jinhwanlazy/hhkb-pcb/firmware/config.h

/*
Copyright 2012 Jun Wako <wakojun@gmail.com>

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
You should have received a copy of the GNU General Public License
along with this program.  If not, see <http://www.gnu.org/licenses/>.
*/

#ifndef CONFIG_H
#define CONFIG_H


/* USB Device descriptor parameter */
#define VENDOR_ID       0xFEED
#define PRODUCT_ID      0x6060
#define DEVICE_VER      0x0001
#define MANUFACTURER    jinhwanlazy
#define PRODUCT         hhkb_s
#define DESCRIPTION     Single_sided_happy_hacking_copy

/* key matrix size */
#define MATRIX_ROWS 5
#define MATRIX_COLS 12

/* define if matrix has ghost */
//#define MATRIX_HAS_GHOST

/* Set 0 if debouncing isn't needed */
#define DEBOUNCE    5

/* Mechanical locking support. Use KC_LCAP, KC_LNUM or KC_LSCR instead in keymap */
#define LOCKING_SUPPORT_ENABLE
/* Locking resynchronize hack */
#define LOCKING_RESYNC_ENABLE

/* key combination for command */
#define IS_COMMAND() ( \
    keyboard_report->mods == (MOD_BIT(KC_LSHIFT) | MOD_BIT(KC_RSHIFT)) \
)



/*
 * Feature disable options
 *  These options are also useful to firmware size reduction.
 */

/* disable debug print */
//#define NO_DEBUG

/* disable print */
//#define NO_PRINT

/* disable action features */
//#define NO_ACTION_LAYER
//#define NO_ACTION_TAPPING
//#define NO_ACTION_ONESHOT
//#define NO_ACTION_MACRO
//#define NO_ACTION_FUNCTION

#endif
