jinhwanlazy/hhkb-pcb/firmware/keymap_common.h

/*
Copyright 2012,2013 Jun Wako <wakojun@gmail.com>

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
You should have received a copy of the GNU General Public License
along with this program.  If not, see <http://www.gnu.org/licenses/>.
*/
#ifndef KEYMAP_COMMON_H
#define KEYMAP_COMMON_H

#include <stdint.h>
#include <stdbool.h>
#include "keycode.h"
#include "action.h"
#include "action_code.h"
#include "action_layer.h"
#include "action_macro.h"
#include "action_util.h"
#include "report.h"
#include "host.h"
#include "print.h"
#include "debug.h"
#include "keymap.h"


#define KEYMAP( \
    K00, K01, K02, K03, K04, K05, K15, K26, K16, K06, K07, K08, K09, K0A, K0B, \
    K10,    K11, K12, K13, K14, K25, K35, K36, K27, K17, K18, K19, K1A,   K1B, \
    K20,      K21, K22, K23, K24, K34, K44, K46, K37, K28, K29, K2A,      K2B, \
    K40,       K30, K31, K32, K33, K43, K47, K48, K49, K38, K39,    K3A,  K3B, \
            K41, K42,                  K45,              K4A, K4B              \
) { \
    { KC_##K00, KC_##K01, KC_##K02, KC_##K03, KC_##K04, KC_##K05, KC_##K06, KC_##K07, KC_##K08, KC_##K09, KC_##K0A, KC_##K0B }, \
    { KC_##K10, KC_##K11, KC_##K12, KC_##K13, KC_##K14, KC_##K15, KC_##K16, KC_##K17, KC_##K18, KC_##K19, KC_##K1A, KC_##K1B }, \
    { KC_##K20, KC_##K21, KC_##K22, KC_##K23, KC_##K24, KC_##K25, KC_##K26, KC_##K27, KC_##K28, KC_##K29, KC_##K2A, KC_##K2B }, \
    { KC_##K30, KC_##K31, KC_##K32, KC_##K33, KC_##K34, KC_##K35, KC_##K36, KC_##K37, KC_##K38, KC_##K39, KC_##K3A, KC_##K3B }, \
    { KC_##K40, KC_##K41, KC_##K42, KC_##K43, KC_##K44, KC_##K45, KC_##K46, KC_##K47, KC_##K48, KC_##K49, KC_##K4A, KC_##K4B }  \
}

#endif
